BoujeeEnjinia1701/rubblejack/cad/drawings/RBJ-DWG-112.pdf

BUILD PLAN SKETCH, PLAN NOT YET BUILT RubbleJack · github.com/BoujeeEnjinia1701/rubblejack

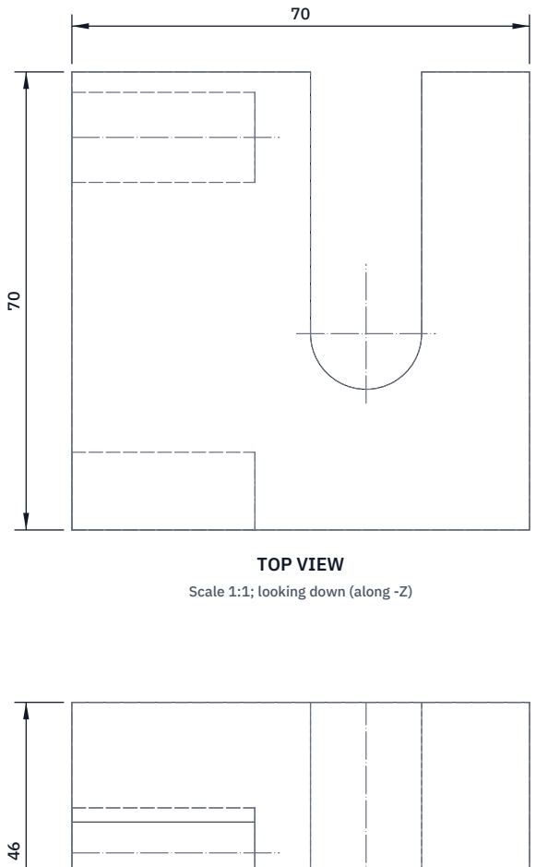
[picture p14: figure]
TOP VIEW; Scale 1:1; looking down (along -Z)

FRONT VIEW
Scale 1:1; looking at the front (along +Y)

RIGHT VIEW
Scale 1:1; looking at the right side (along -X)

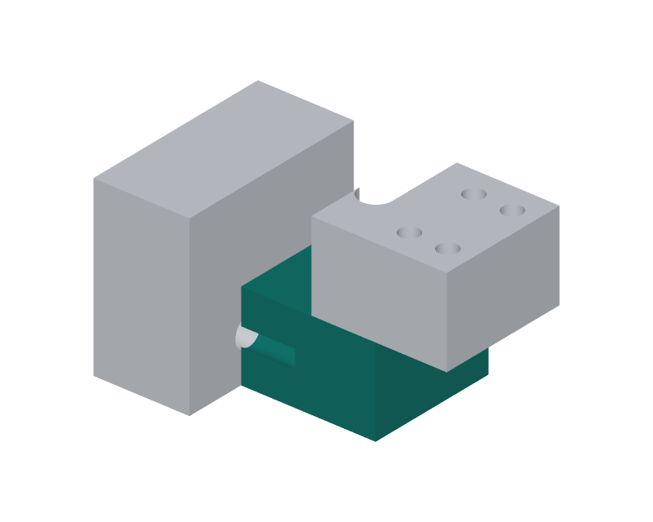
[picture p15: figure]

WHERE IT GOES
This part in colour, its neighbours in grey

HOW TO MAKE IT AND HOW IT FITS
Block 70 long x 70 wide x 45.5 tall (the lower half of the shear).
U notch 17 wide, its round bottom centred 45 mm from the back face, open to the top long edge. The notch's back wall pushes the bar. Back face: two M16 holes, 28 deep, matching the carrier's holes. Machine soft, heat treat, then grind the top face flat and the
notch edges sharp and square: this face slides past the fixed blade. Check: top face flat to 0.05 mm on a surface plate.
REV | DESCRIPTION | DATE | BY
P1 | Making sketch for the prototype build plan | 2026-10-03 | AC
RUBBLEJACK | github.com/BoujeeEnjinia1701/rubblejack

## RubbleJack moving blade: making sketch

DRAWING NO.
RBJ-DWG-112

REV
P1

SHEET
1 of 1

SIZE

## ANSI B

SCALE
1:1

UNITS
mm
PROJECTION | DATE
2026-10-03

DRAWN
Amish Chadha

MATERIAL / NOTES
S7 shock-resisting tool steel, hardened 54 to 56 HRC
Licensed CERN-OHL-S-2.0 · Design Molecule Lab · designmolecule.com | Generated from cad/src; do not edit by hand
