BoujeeEnjinia1701/rubblejack/cad/drawings/RBJ-DWG-113.pdf

BUILD PLAN SKETCH, PLAN NOT YET BUILT RubbleJack · github.com/BoujeeEnjinia1701/rubblejack

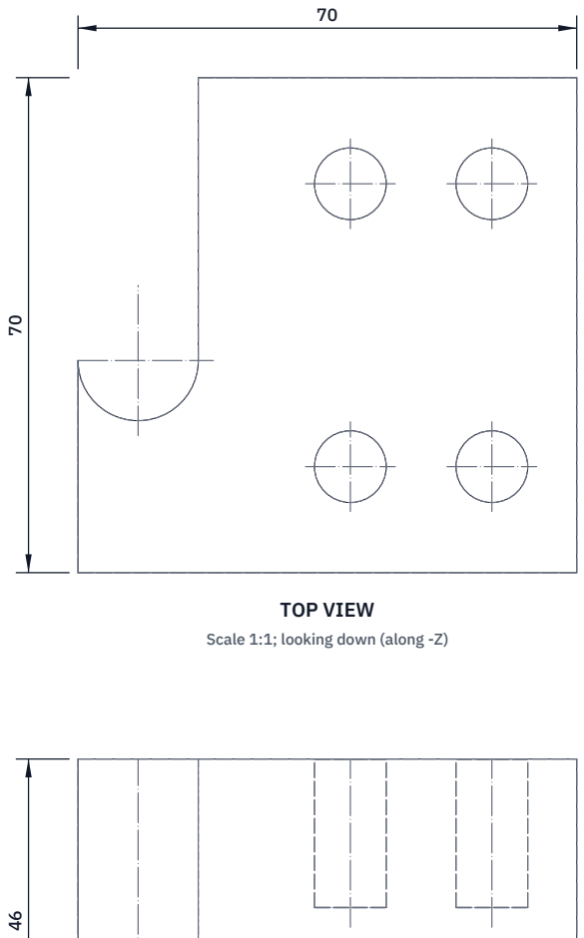
[picture p16: figure]
TOP VIEW; Scale 1:1; looking down (along -Z)

FRONT VIEW
Scale 1:1; looking at the front (along +Y)

RIGHT VIEW
Scale 1:1; looking at the right side (along -X)

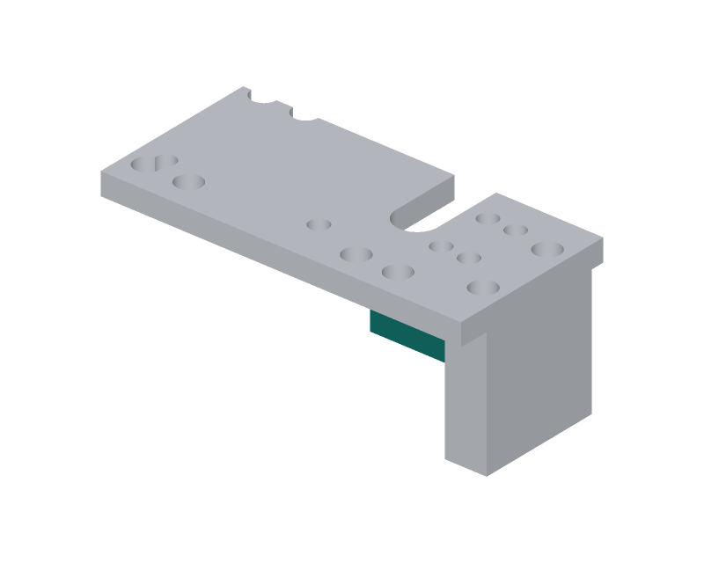
[picture p17: figure]

WHERE IT GOES
This part in colour, its neighbours in grey

HOW TO MAKE IT AND HOW IT FITS
Block 70.5 long x 70 wide x 45.8 tall (the upper half).
U notch 17 wide, its round bottom 8.5 mm from the back face,
in line with the moving blade's notch.
Top face: four M12 holes 20 deep at 30 and 50 mm in front of the
notch centre, 15 mm toward the lower edge and 25 mm toward the upper. Grind the bottom face flat and the notch edges sharp; the front
face bears on the nose block and must be square.
Fit: 0.2 mm above the moving blade; shim under the upper plate if needed.
REV | DESCRIPTION | DATE | BY
P1 | Making sketch for the prototype build plan | 2026-10-03 | AC
RUBBLEJACK | github.com/BoujeeEnjinia1701/rubblejack

## RubbleJack fixed blade: making sketch

DRAWING NO.
RBJ-DWG-113

REV
P1

SHEET
1 of 1

SIZE

## ANSI B

SCALE
1:1

UNITS
mm
PROJECTION | DATE
2026-10-03

DRAWN
Amish Chadha

MATERIAL / NOTES
S7 shock-resisting tool steel, hardened 54 to 56 HRC
Licensed CERN-OHL-S-2.0 · Design Molecule Lab · designmolecule.com | Generated from cad/src; do not edit by hand
