BoujeeEnjinia1701/rubblejack/cad/drawings/RBJ-DWG-116.pdf

BUILD PLAN SKETCH, PLAN NOT YET BUILT RubbleJack · github.com/BoujeeEnjinia1701/rubblejack

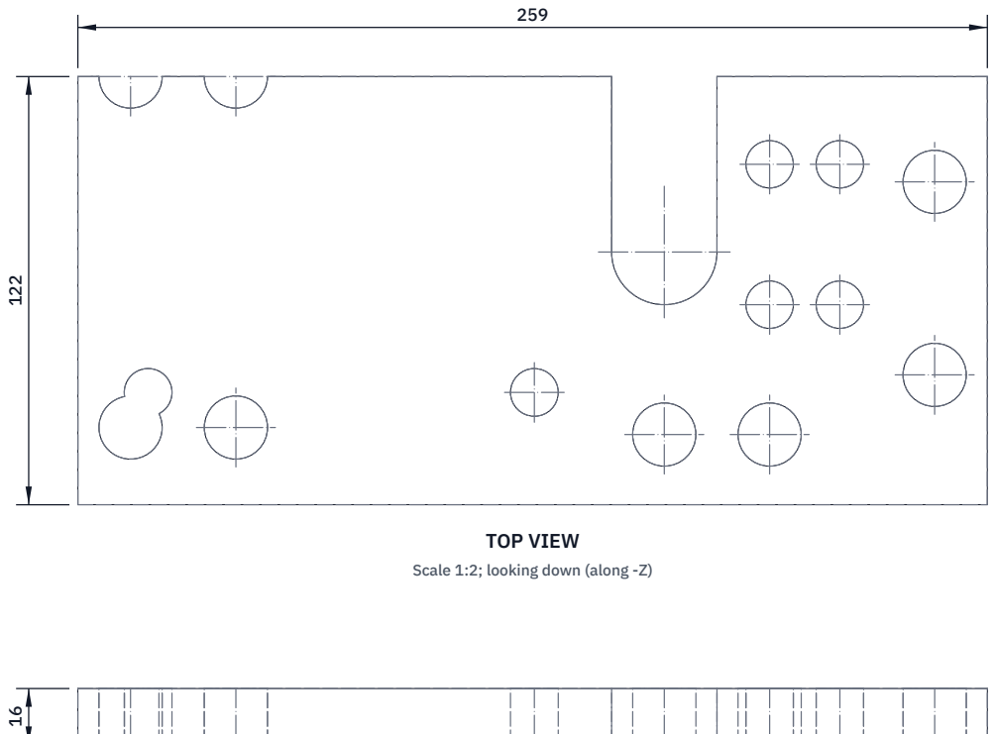
[picture p18: figure]
TOP VIEW; Scale 1:2; looking down (along -Z)

FRONT VIEW
Scale 1:2; looking at the front (along +Y)

RIGHT VIEW
Scale 1:2; looking at the right side (along -X)

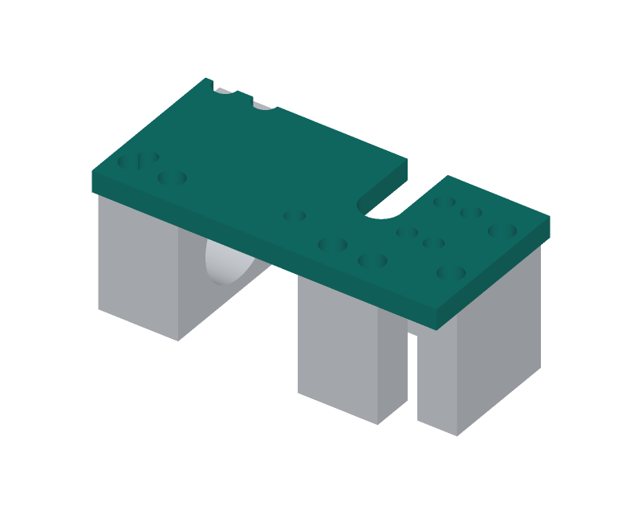
[picture p19: figure]

WHERE IT GOES
This part in colour, its neighbours in grey

HOW TO MAKE IT AND HOW IT FITS
Two plates 259 x 122, 16 mm, laser cut. Sizes from the back edge. Hook 30 wide, centred 167 mm from the back edge; its round bottom 57 mm up from the lower edge; open to the upper edge. 18 mm holes: adapter 15 and 45 from the back, 50 each side of the axis (72 up from the lower edge); nose at 244;
stop at 167 and 197, 20 up from the lower edge.
Upper plate only: four 13.5 mm fixed blade holes and two 13.6 mm handle holes (drawn); the lower plate has neither.
Drill the shared holes with both plates clamped together.
Check: hooks line up when the plates are stacked.
REV | DESCRIPTION | DATE | BY
P1 | Making sketch for the prototype build plan | 2026-10-03 | AC
RUBBLEJACK | github.com/BoujeeEnjinia1701/rubblejack

## RubbleJack cutter plate (make 2): making sketch

DRAWING NO.
RBJ-DWG-116

REV
P1

SHEET
1 of 1

SIZE

## ANSI B

SCALE
1:2

UNITS
mm
PROJECTION | DATE
2026-10-03

DRAWN
Amish Chadha

MATERIAL / NOTES
S690QL steel plate, 16 mm
Licensed CERN-OHL-S-2.0 · Design Molecule Lab · designmolecule.com | Generated from cad/src; do not edit by hand
