BoujeeEnjinia1701/rubblejack/cad/drawings/RBJ-DWG-001.png

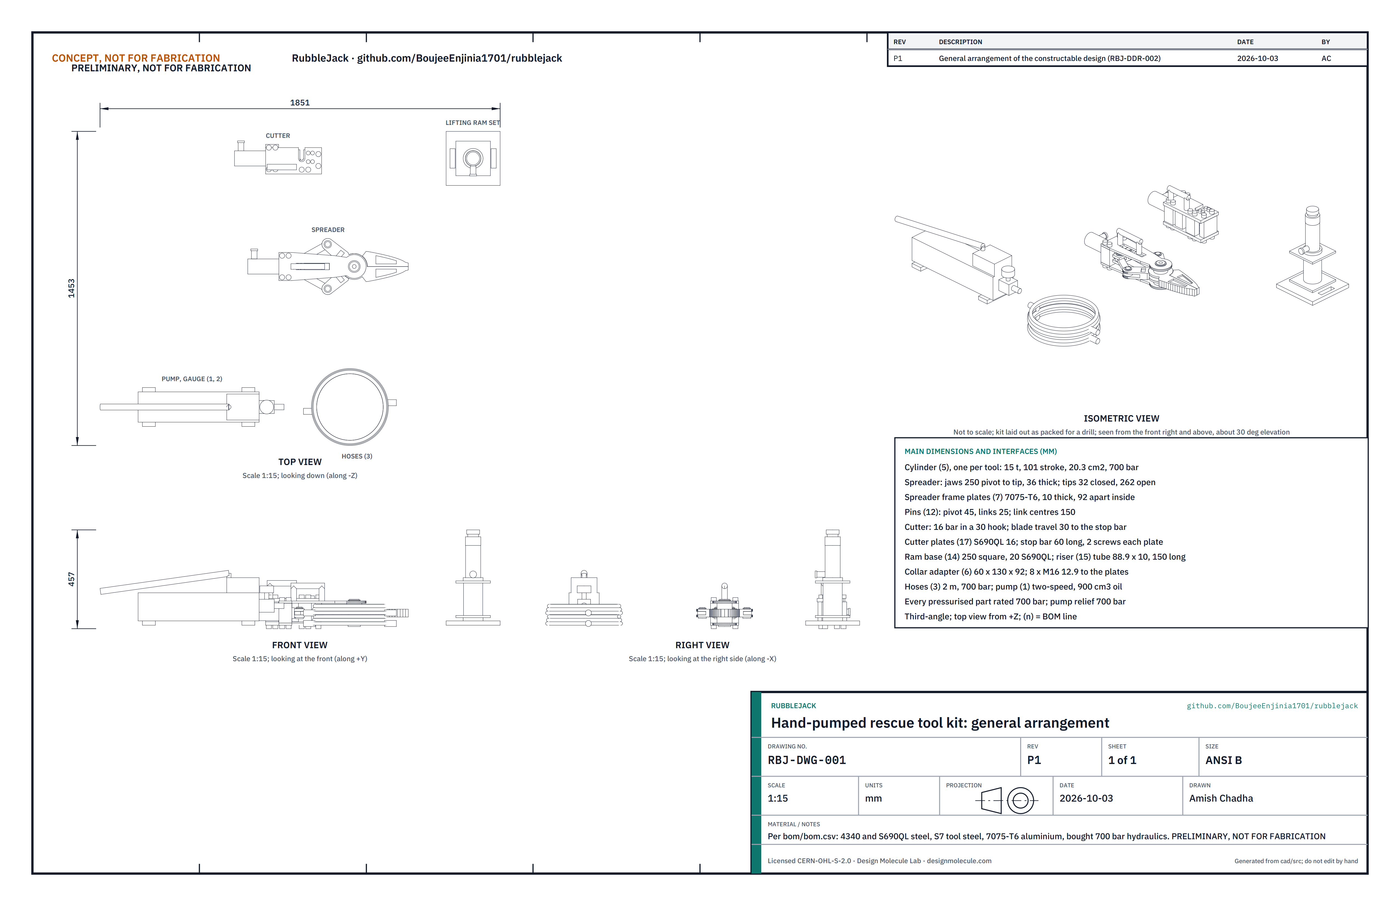
cad/drawings/RBJ-DWG-001.png
