BoujeeEnjinia1701/rubblejack/media/card.png

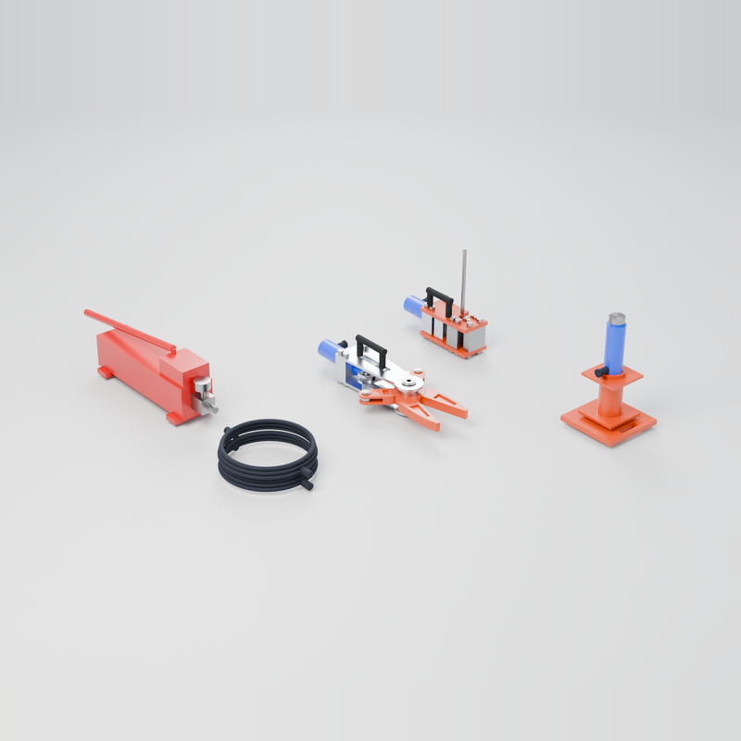
media/card.png
