BoujeeEnjinia1701/rubblejack/media/render-detail.png

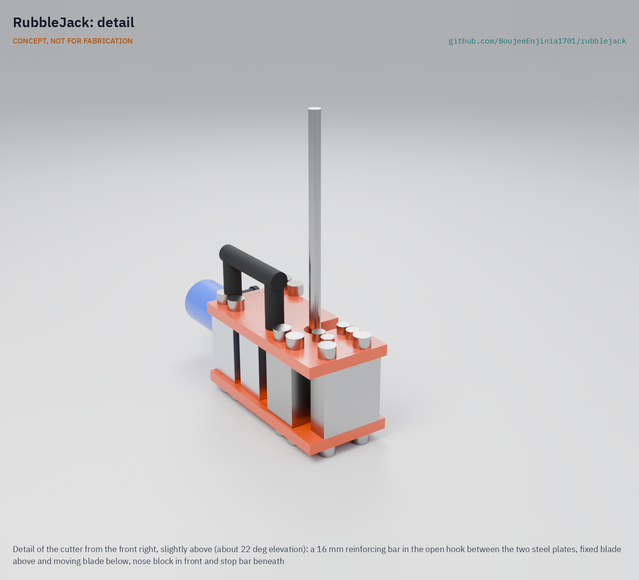
media/render-detail.png
