BoujeeEnjinia1701/rubblejack/media/render-exploded.png

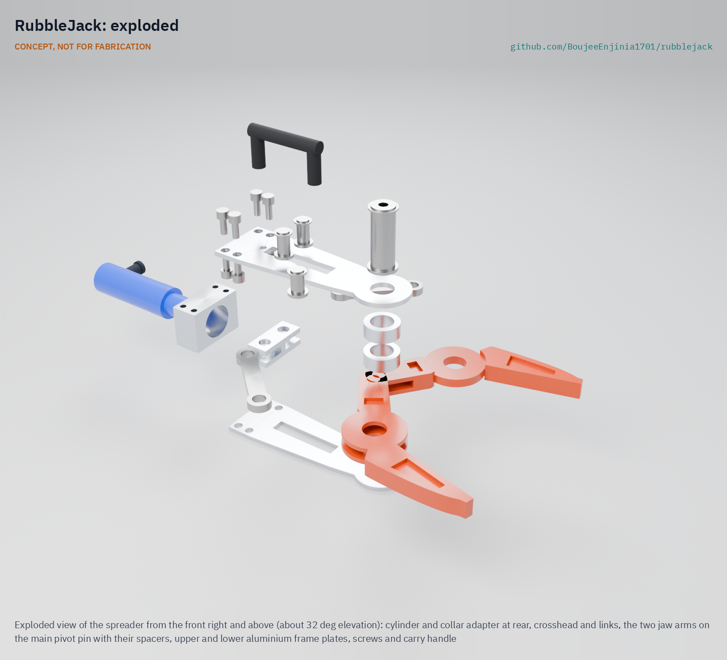
media/render-exploded.png
