BoujeeEnjinia1701/rubblejack/media/social-preview.png

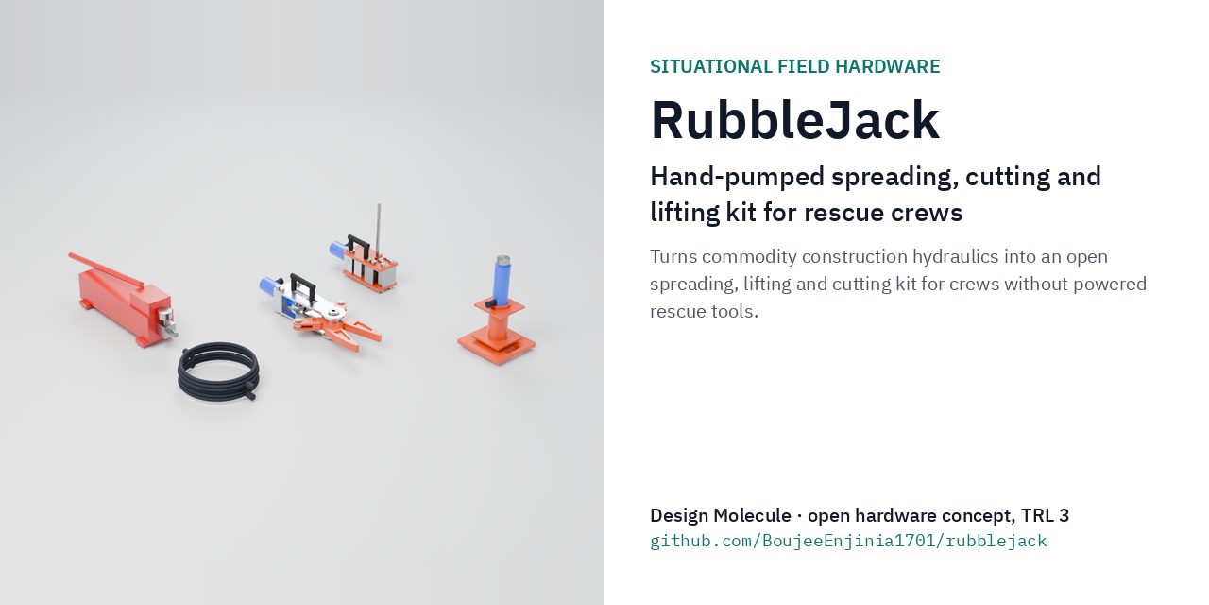
media/social-preview.png
