BoujeeEnjinia1701/rubblejack/cad/drawings/RBJ-DWG-111.pdf

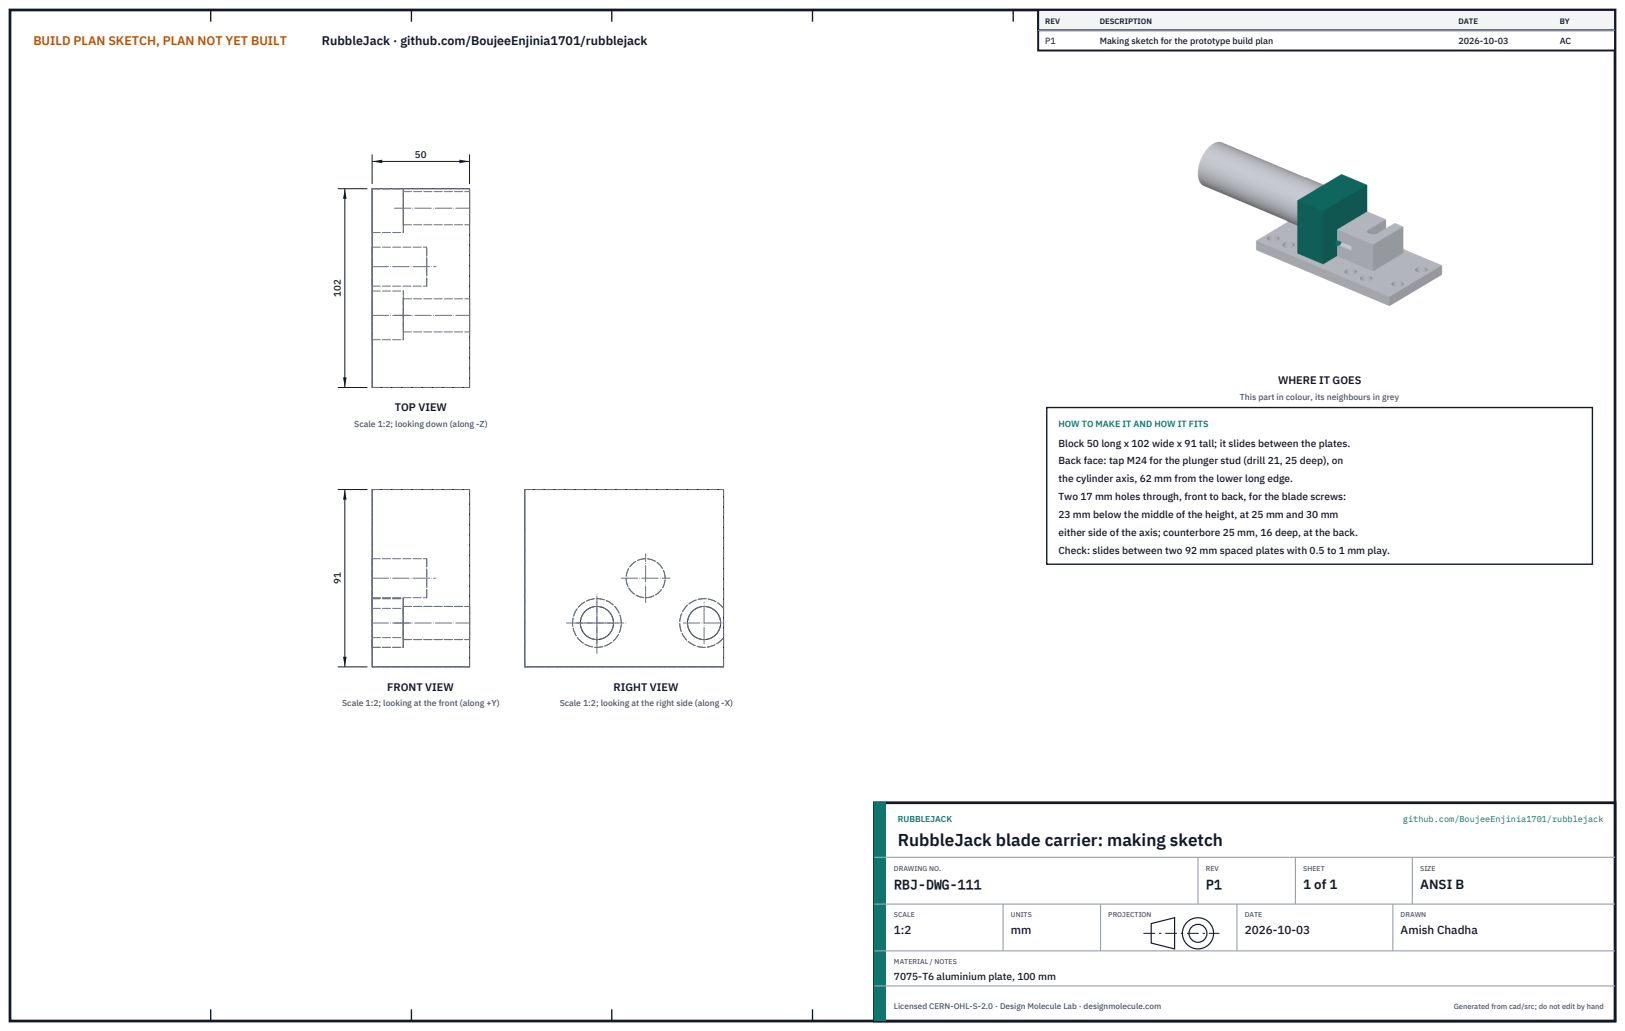
[picture p83: page 1]
BUILD PLAN SKETCH, PLAN NOT YET BUILT; RubbleJack · github.com/BoujeeEnjinia1701/rubblejack; FRONT VIEW; TOP VIEW; RIGHT VIEW; REV; DESCRIPTION; DATE; Making sketch for the prototype build plan; RUBBLEJACK; github.com/BoujeeEnjinia1701/rubblejack; DRAWING NO. RBJ-DWG-111; REV P1; SHEET 1 of 1; SIZE ANSI B; SCALE 1:2; UNITS mm; PROJECTION; DRAWN Amish Chadha; Licensed CERN-OHL-S-2.0 · Design Molecule Lab · designmolecule.com; Generated from cad/src; do not edit by hand

WHERE IT GOES

This part in colour, its neighbours in grey

Scale 1:2; looking down (along -Z)

HOW TO MAKE IT AND HOW IT FITS
Block 50 long x 102 wide x 91 tall; it slides between the plates.
Back face: tap M24 for the plunger stud (drill 21, 25 deep), on
the cylinder axis, 62 mm from the lower long edge.
Two 17 mm holes through, front to back, for the blade screws:
23 mm below the middle of the height, at 25 mm and 30 mm
either side of the axis; counterbore 25 mm, 16 deep, at the back.
Check: slides between two 92 mm spaced plates with 0.5 to 1 mm play.

Scale 1:2; looking at the front (along +Y)

Scale 1:2; looking at the right side (along -X)

RubbleJack blade carrier: making sketch

MATERIAL / NOTES
7075-T6 aluminium plate, 100 mm
