BoujeeEnjinia1701/rubblejack/cad/drawings/RBJ-DWG-114.pdf

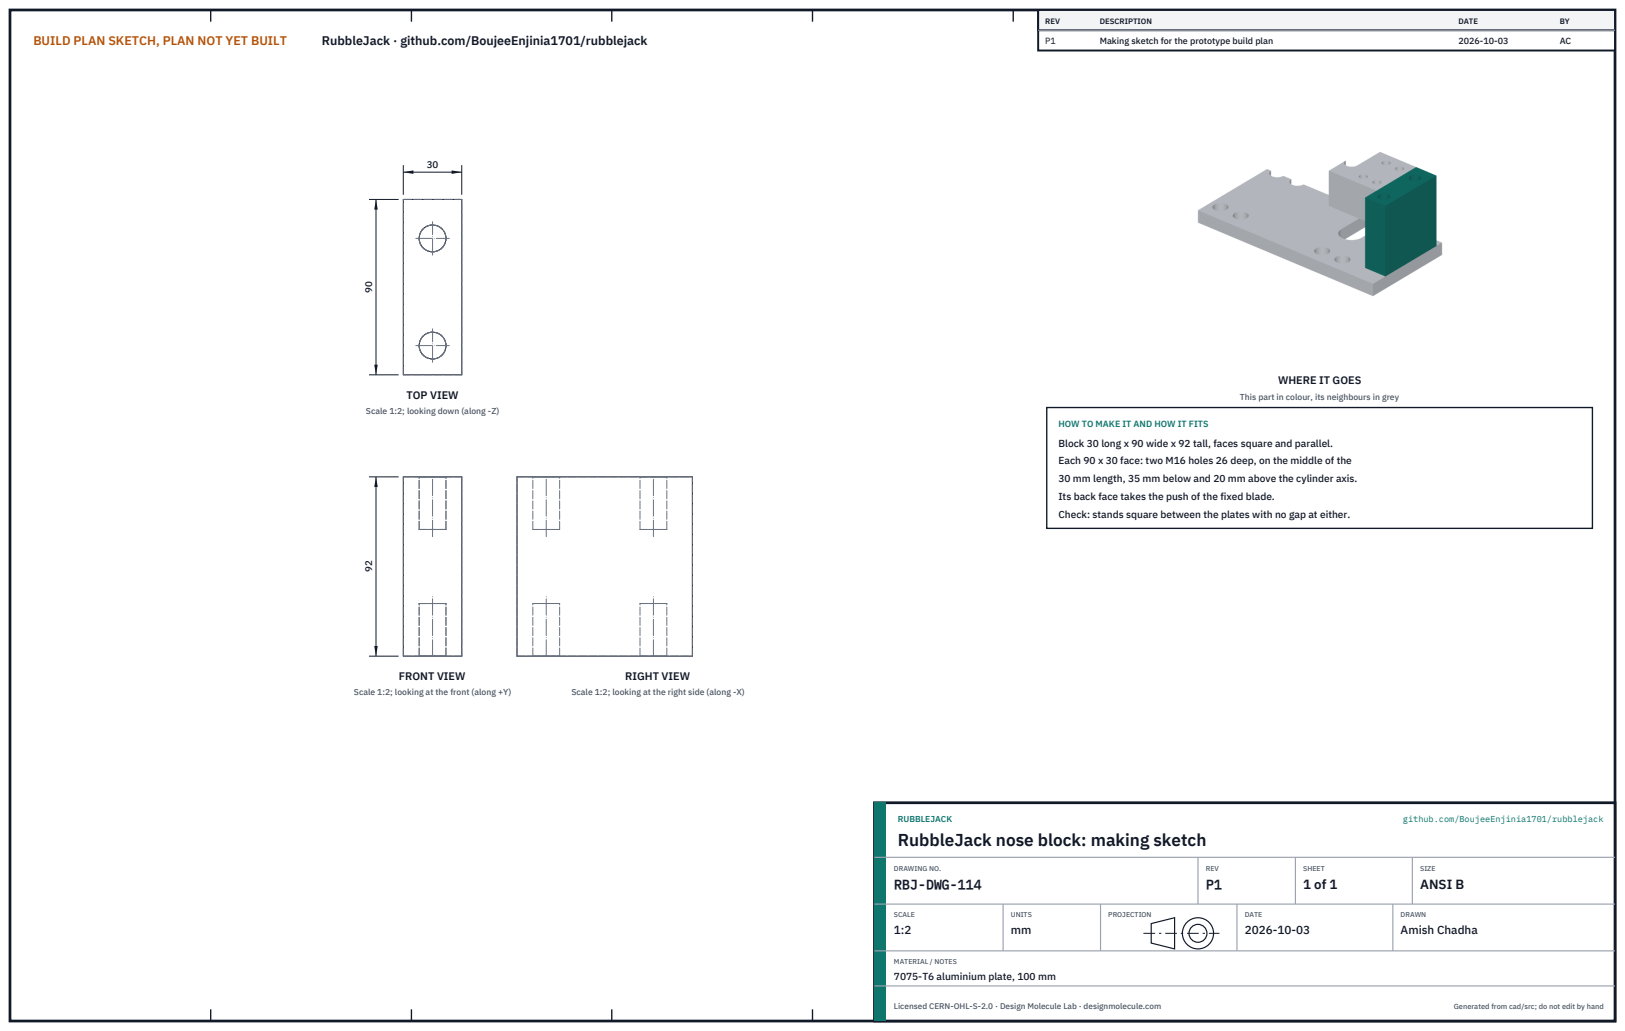
[picture p84: page 1]
BUILD PLAN SKETCH, PLAN NOT YET BUILT; RubbleJack · github.com/BoujeeEnjinia1701/rubblejack; FRONT VIEW; TOP VIEW; RIGHT VIEW; REV; DESCRIPTION; DATE; Making sketch for the prototype build plan; RUBBLEJACK; github.com/BoujeeEnjinia1701/rubblejack; DRAWING NO. RBJ-DWG-114; REV P1; SHEET 1 of 1; SIZE ANSI B; SCALE 1:2; UNITS mm; PROJECTION; DRAWN Amish Chadha; Licensed CERN-OHL-S-2.0 · Design Molecule Lab · designmolecule.com; Generated from cad/src; do not edit by hand

WHERE IT GOES

This part in colour, its neighbours in grey

Scale 1:2; looking down (along -Z)

HOW TO MAKE IT AND HOW IT FITS
Block 30 long x 90 wide x 92 tall, faces square and parallel.
Each 90 x 30 face: two M16 holes 26 deep, on the middle of the
30 mm length, 35 mm below and 20 mm above the cylinder axis.
Its back face takes the push of the fixed blade.
Check: stands square between the plates with no gap at either.

Scale 1:2; looking at the front (along +Y)

Scale 1:2; looking at the right side (along -X)

RubbleJack nose block: making sketch

MATERIAL / NOTES
7075-T6 aluminium plate, 100 mm
