BoujeeEnjinia1701/rubblejack/cad/drawings/RBJ-DWG-115.pdf

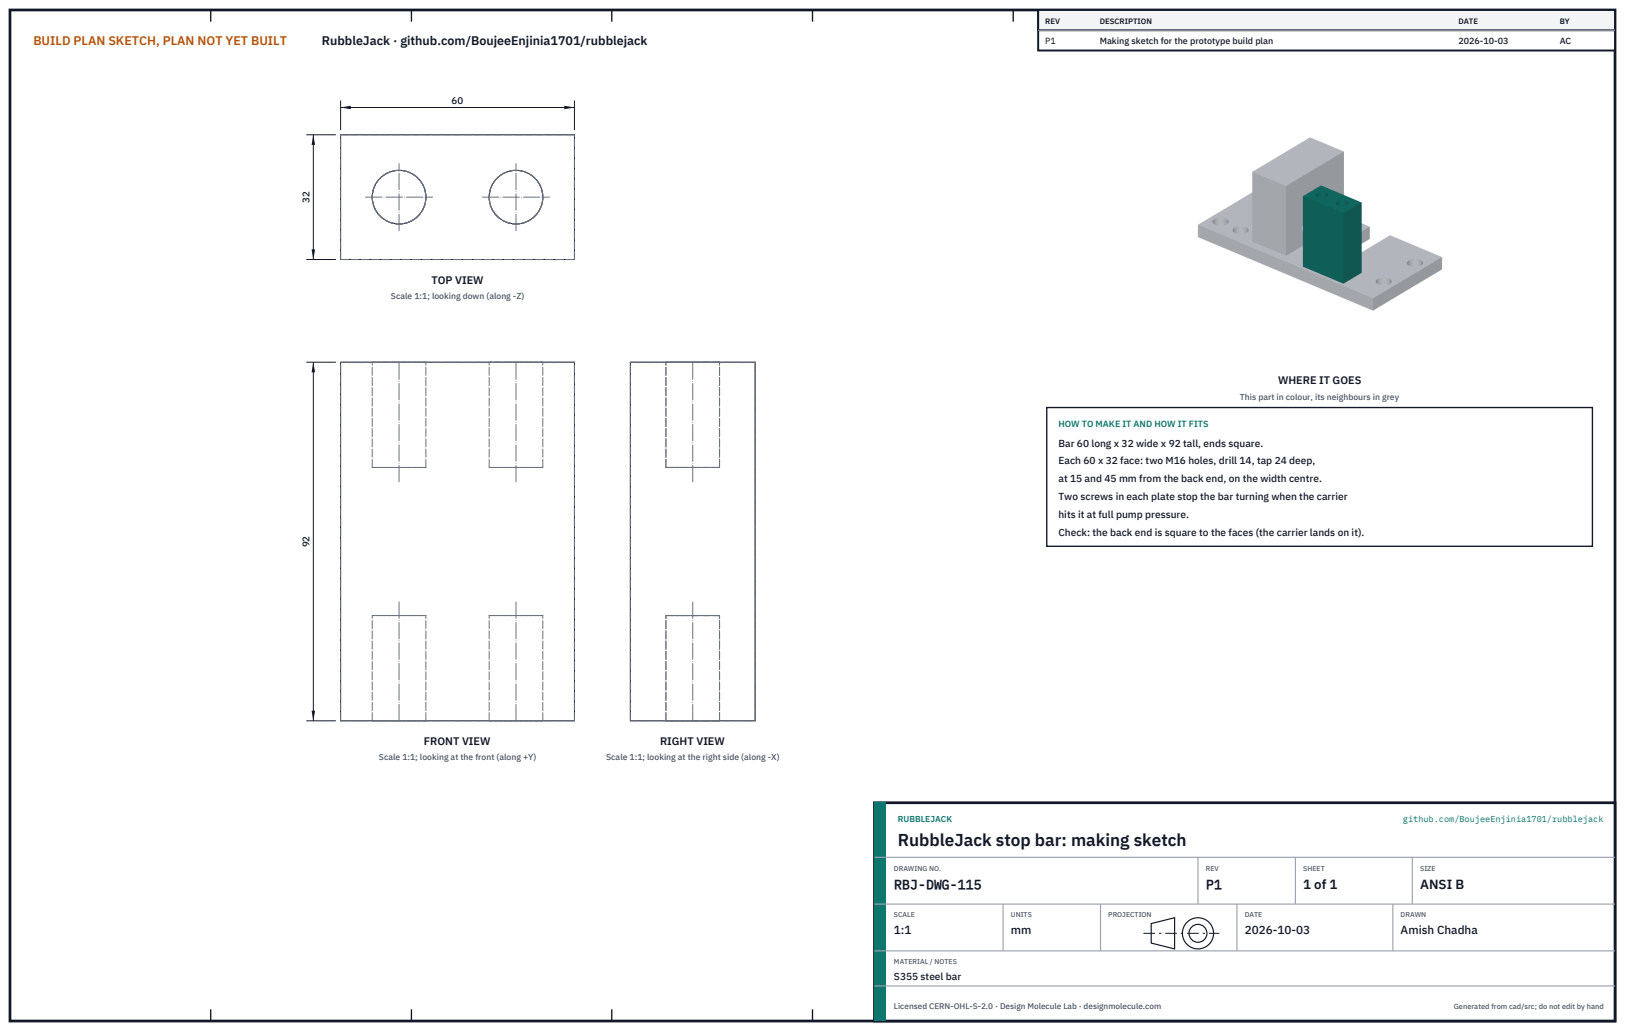
[picture p85: page 1]
BUILD PLAN SKETCH, PLAN NOT YET BUILT; RubbleJack · github.com/BoujeeEnjinia1701/rubblejack; FRONT VIEW; TOP VIEW; RIGHT VIEW; REV; DESCRIPTION; DATE; Making sketch for the prototype build plan; RUBBLEJACK; github.com/BoujeeEnjinia1701/rubblejack; DRAWING NO. RBJ-DWG-115; REV P1; SHEET 1 of 1; SIZE ANSI B; SCALE 1:1; UNITS mm; PROJECTION; DRAWN Amish Chadha; MATERIAL / NOTES S355 steel bar; Licensed CERN-OHL-S-2.0 · Design Molecule Lab · designmolecule.com; Generated from cad/src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

Scale 1:1; looking down (along -Z)

WHERE IT GOES

This part in colour, its neighbours in grey

HOW TO MAKE IT AND HOW IT FITS
Bar 60 long x 32 wide x 92 tall, ends square.
Each 60 x 32 face: two M16 holes, drill 14, tap 24 deep,
at 15 and 45 mm from the back end, on the width centre.
Two screws in each plate stop the bar turning when the carrier
hits it at full pump pressure.
Check: the back end is square to the faces (the carrier lands on it).

Scale 1:1; looking at the front (along +Y)

Scale 1:1; looking at the right side (along -X)

RubbleJack stop bar: making sketch
