BoujeeEnjinia1701/rubblejack/cad/drawings/RBJ-DWG-117.pdf

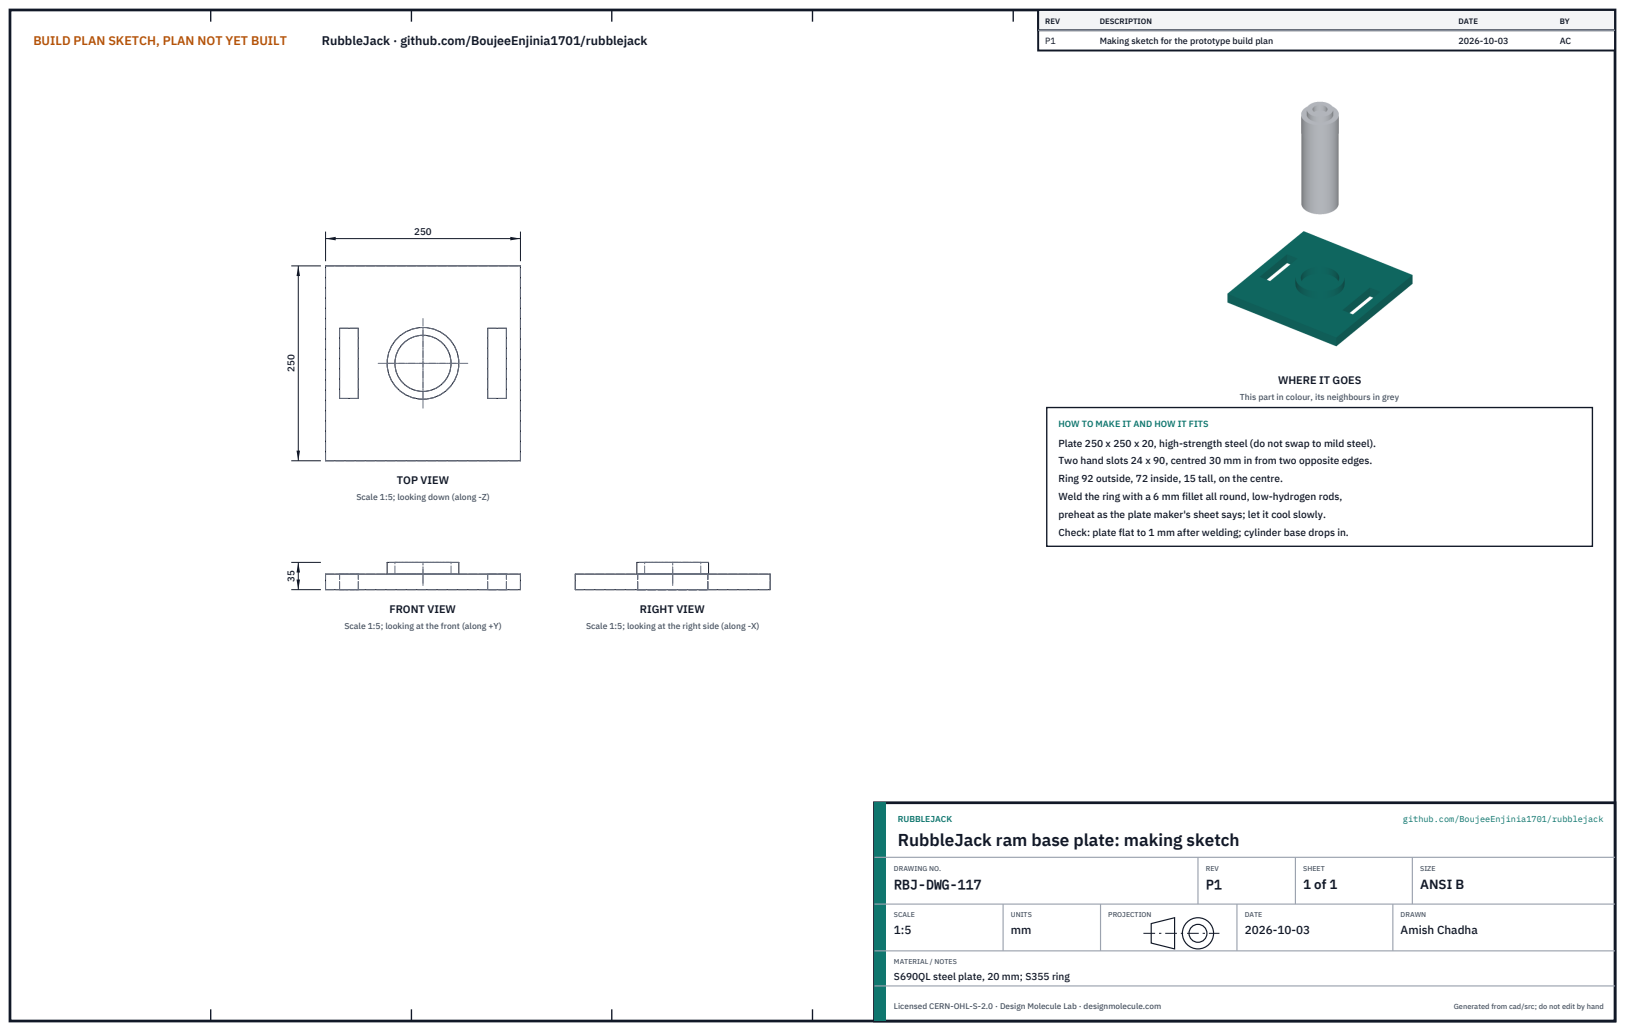
[picture p86: page 1]
BUILD PLAN SKETCH, PLAN NOT YET BUILT; RubbleJack · github.com/BoujeeEnjinia1701/rubblejack; FRONT VIEW; TOP VIEW; RIGHT VIEW; REV; DESCRIPTION; DATE; Making sketch for the prototype build plan; RUBBLEJACK; github.com/BoujeeEnjinia1701/rubblejack; DRAWING NO. RBJ-DWG-117; REV P1; SHEET 1 of 1; SIZE ANSI B; SCALE 1:5; UNITS mm; PROJECTION; DRAWN Amish Chadha; Licensed CERN-OHL-S-2.0 · Design Molecule Lab · designmolecule.com; Generated from cad/src; do not edit by hand

WHERE IT GOES

This part in colour, its neighbours in grey

HOW TO MAKE IT AND HOW IT FITS
Plate 250 x 250 x 20, high-strength steel (do not swap to mild steel).
Two hand slots 24 x 90, centred 30 mm in from two opposite edges.
Ring 92 outside, 72 inside, 15 tall, on the centre.
Weld the ring with a 6 mm fillet all round, low-hydrogen rods,
preheat as the plate maker's sheet says; let it cool slowly.
Check: plate flat to 1 mm after welding; cylinder base drops in.

Scale 1:5; looking down (along -Z)

Scale 1:5; looking at the front (along +Y)

Scale 1:5; looking at the right side (along -X)

RubbleJack ram base plate: making sketch

MATERIAL / NOTES
S690QL steel plate, 20 mm; S355 ring
