BoujeeEnjinia1701/rubblejack/cad/drawings/RBJ-DWG-118.pdf

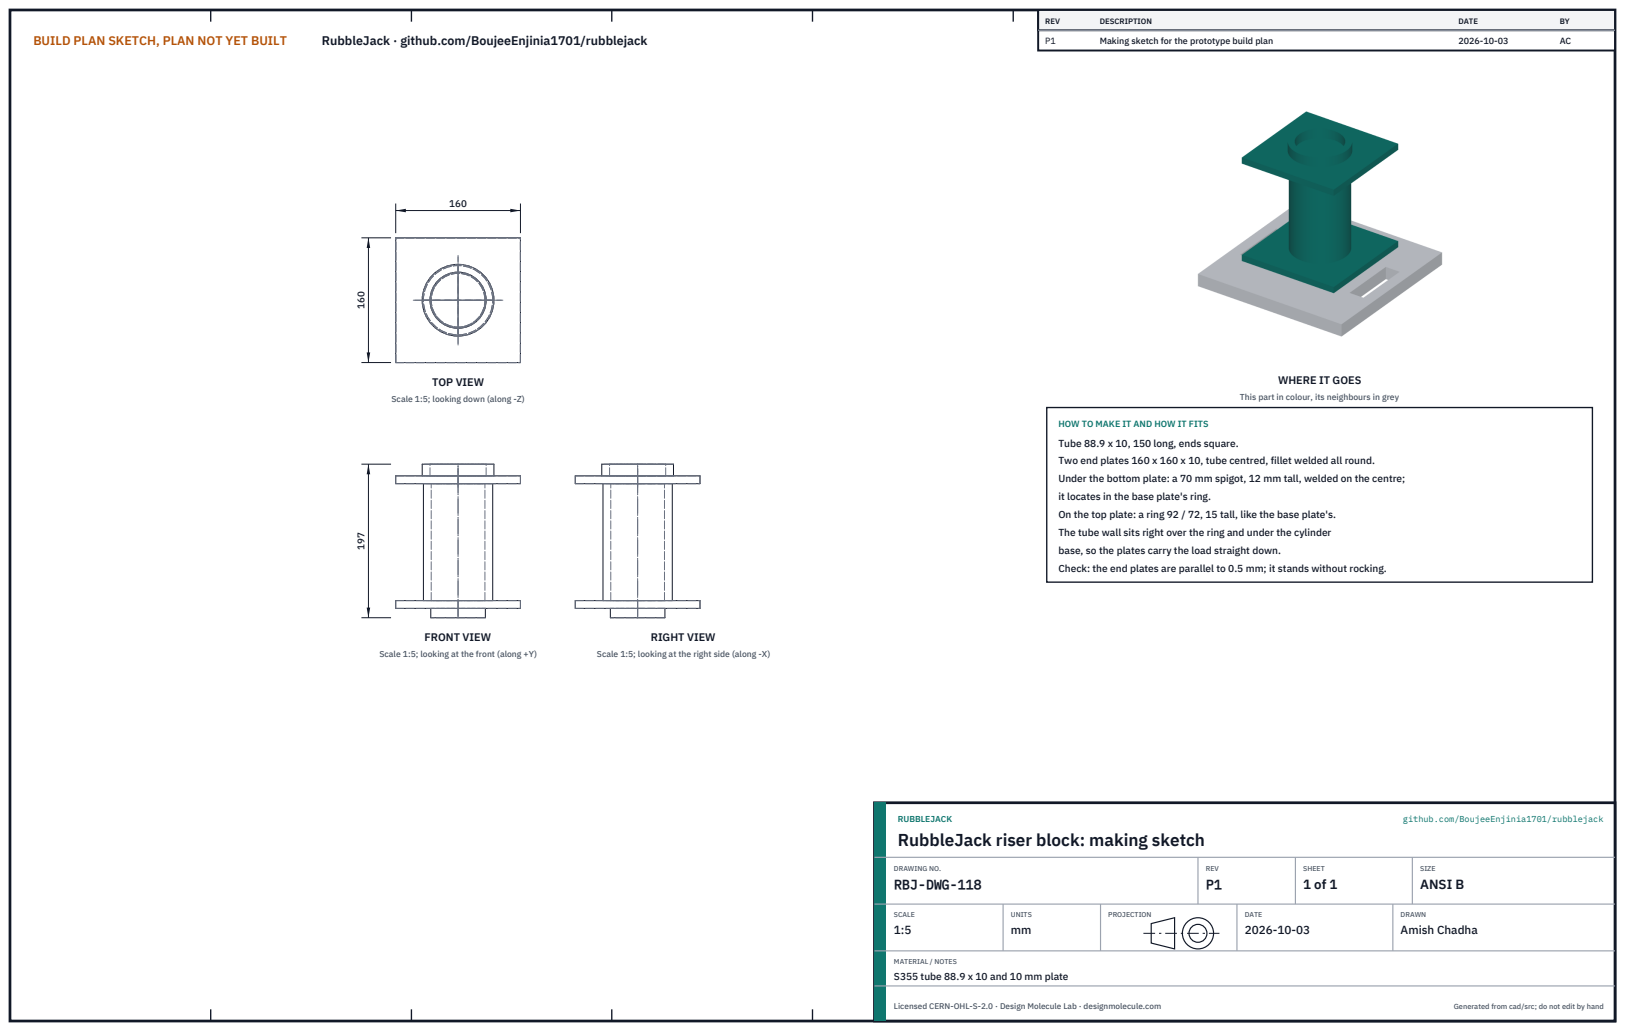
[picture p87: page 1]
BUILD PLAN SKETCH, PLAN NOT YET BUILT; RubbleJack · github.com/BoujeeEnjinia1701/rubblejack; FRONT VIEW; TOP VIEW; RIGHT VIEW; REV; DESCRIPTION; DATE; Making sketch for the prototype build plan; RUBBLEJACK; github.com/BoujeeEnjinia1701/rubblejack; DRAWING NO. RBJ-DWG-118; REV P1; SHEET 1 of 1; SIZE ANSI B; SCALE 1:5; UNITS mm; PROJECTION; DRAWN Amish Chadha; Licensed CERN-OHL-S-2.0 · Design Molecule Lab · designmolecule.com; Generated from cad/src; do not edit by hand

WHERE IT GOES

Scale 1:5; looking down (along -Z)

This part in colour, its neighbours in grey

HOW TO MAKE IT AND HOW IT FITS
Tube 88.9 x 10, 150 long, ends square.
Two end plates 160 x 160 x 10, tube centred, fillet welded all round.
Under the bottom plate: a 70 mm spigot, 12 mm tall, welded on the centre;
it locates in the base plate's ring.
On the top plate: a ring 92 / 72, 15 tall, like the base plate's.
The tube wall sits right over the ring and under the cylinder
base, so the plates carry the load straight down.
Check: the end plates are parallel to 0.5 mm; it stands without rocking.

Scale 1:5; looking at the front (along +Y)

Scale 1:5; looking at the right side (along -X)

RubbleJack riser block: making sketch

MATERIAL / NOTES
S355 tube 88.9 x 10 and 10 mm plate
